carlosdelfino/synap.sys/fontes/arduino/teste_laser/teste_laser.ino

#include <Servo.h>

/*
  Blink
  Turns on an LED on for one second, then off for one second, repeatedly.

  This example code is in the public domain.
 */

// Pin 13 has an LED connected on most Arduino boards.
// give it a name:
int led = 13;


Servo servos[5];  // create servo object to control a servo

// the setup routine runs once when you press reset:
void setup() {
  // initialize the digital pin as an output.
  pinMode(led, OUTPUT);
  for(int i = 0; i<5;i++){ 
    servos[i].attach(12-i);
  }
}

// the loop routine runs over and over again forever:
void loop() {
  digitalWrite(led, HIGH);   // turn the LED on (HIGH is the voltage level)
  delay(100);               // wait for a second
  digitalWrite(led, LOW);    // turn the LED off by making the voltage LOW
  delay(100);               // wait for a second
  for (int led = 2 ; led < 7; led++) {
    digitalWrite(led, HIGH);   // turn the LED on (HIGH is the voltage level)
    delay(200);               // wait for a second
    digitalWrite(led, LOW);    // turn the LED off by making the voltage LOW
    delay(100);               // wait for a second
    servos[led-2].write(map(rand(),0,RAND_MAX,0,180));
  }
}
